ElectronicCats/badge-hackgdl-2025/firmware/components/tamalib_idf/bitmaps.h

static const uint8_t bitmaps[] = {
    0x00, 0x20, 0x00, 0x10, 0x00, 0xFE, 0x01, 0xFB, 0x01, 0xFD, 0x01, 0xFF,
    0x01, 0xFF, 0x00, 0xFE, 0x00, 0x6C, 0x00, 0x10, 0x00, 0x82, 0x00, 0x38,
    0x00, 0x7C, 0x00, 0x7D, 0x01, 0x7C, 0x00, 0x38, 0x00, 0x82, 0x00, 0x10,
    0x00, 0x04, 0x00, 0x06, 0x01, 0xFF, 0x00, 0x06, 0x00, 0x44, 0x00, 0xC0,
    0x01, 0xFF, 0x00, 0xC0, 0x00, 0x40, 0x00, 0xEE, 0x01, 0x11, 0x01, 0x00,
    0x01, 0x02, 0x01, 0x07, 0x00, 0x82, 0x00, 0x40, 0x00, 0x28, 0x00, 0x10,
    0x00, 0x20, 0x00, 0x02, 0x00, 0x98, 0x00, 0x1C, 0x00, 0x64, 0x00, 0xFE,
    0x00, 0xFE, 0x01, 0x8F, 0x01, 0xFF, 0x00, 0x1C, 0x00, 0x22, 0x00, 0x41,
    0x00, 0x41, 0x00, 0x41, 0x00, 0x22, 0x00, 0x5C, 0x00, 0x80, 0x01, 0x00,
    0x00, 0x1E, 0x00, 0x3F, 0x00, 0x33, 0x00, 0x2F, 0x00, 0x7F, 0x01, 0x3F,
    0x00, 0x9F, 0x01, 0x3E, 0x00, 0x0C, 0x00, 0x7C, 0x00, 0x82, 0x01, 0x11,
    0x01, 0x11, 0x01, 0x11, 0x01, 0x01, 0x01, 0x11, 0x00, 0x82, 0x00, 0x7C};
